rc-kid/rckid/cartridges/demo/sd/files/images/backgrounds/background16.png

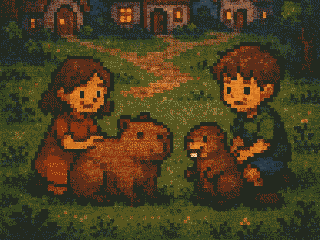
cartridges/demo/sd/files/images/backgrounds/background16.png
