rc-kid/rckid/cartridges/demo/sd/files/images/backgrounds/capybeaver.png

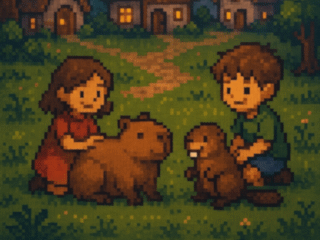
cartridges/demo/sd/files/images/backgrounds/capybeaver.png
