rc-kid/rckid/docs/photos/mkIII-back.jpeg

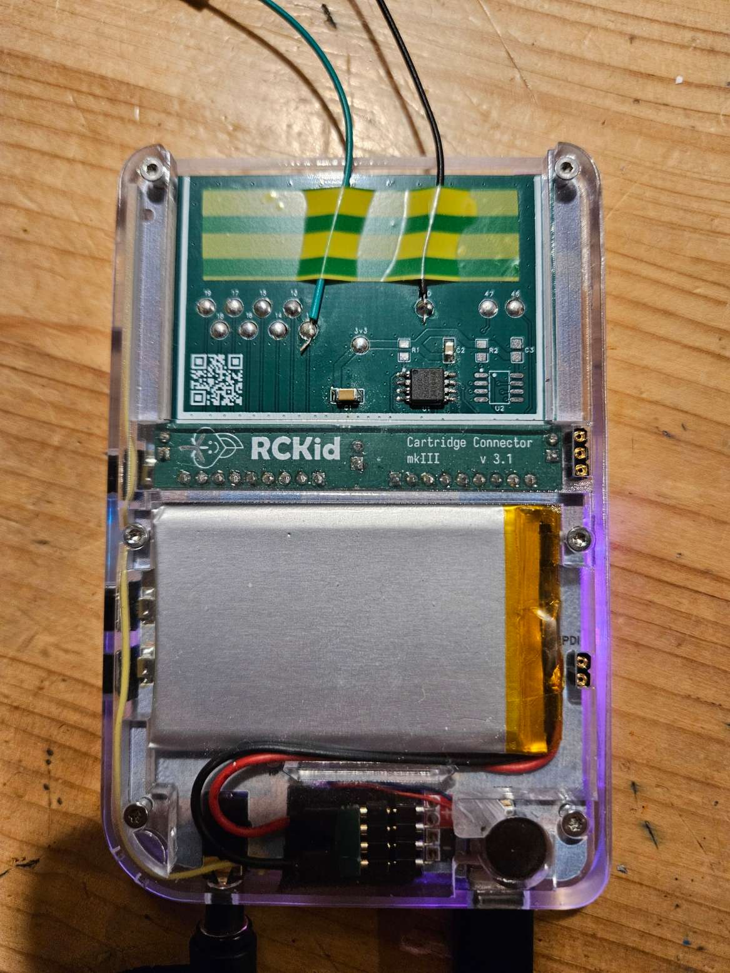
docs/photos/mkIII-back.jpeg
