rc-kid/rckid/docs/photos/mkIII-dark.jpeg

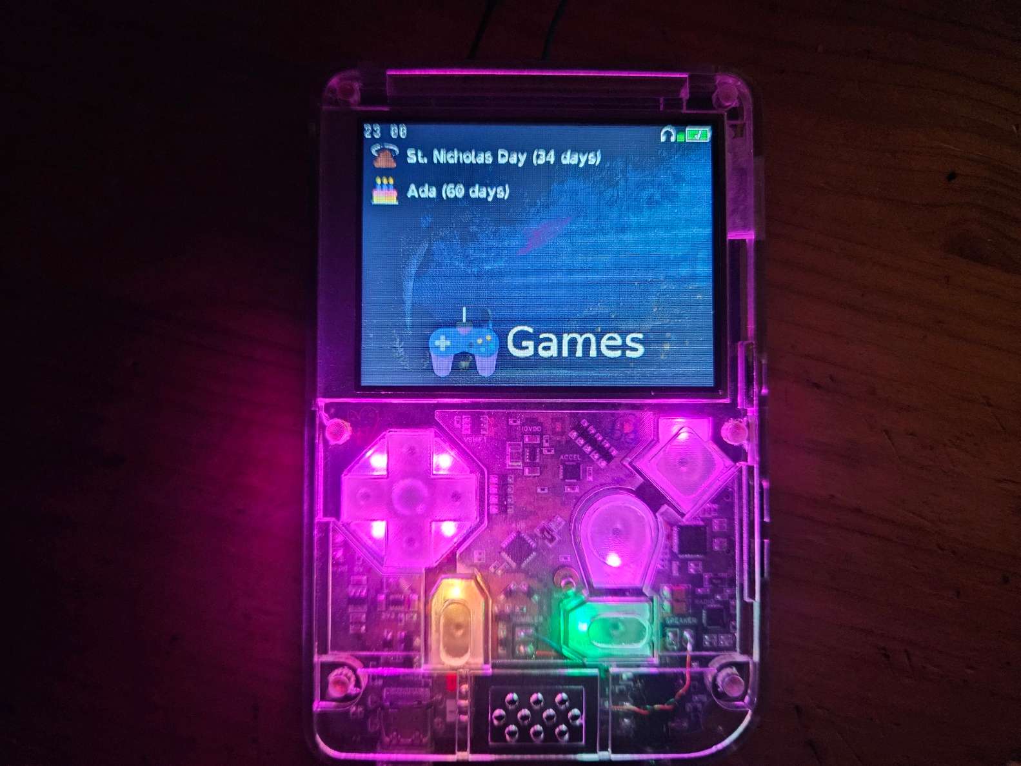
docs/photos/mkIII-dark.jpeg
