rc-kid/rckid/docs/photos/rckid.jpg

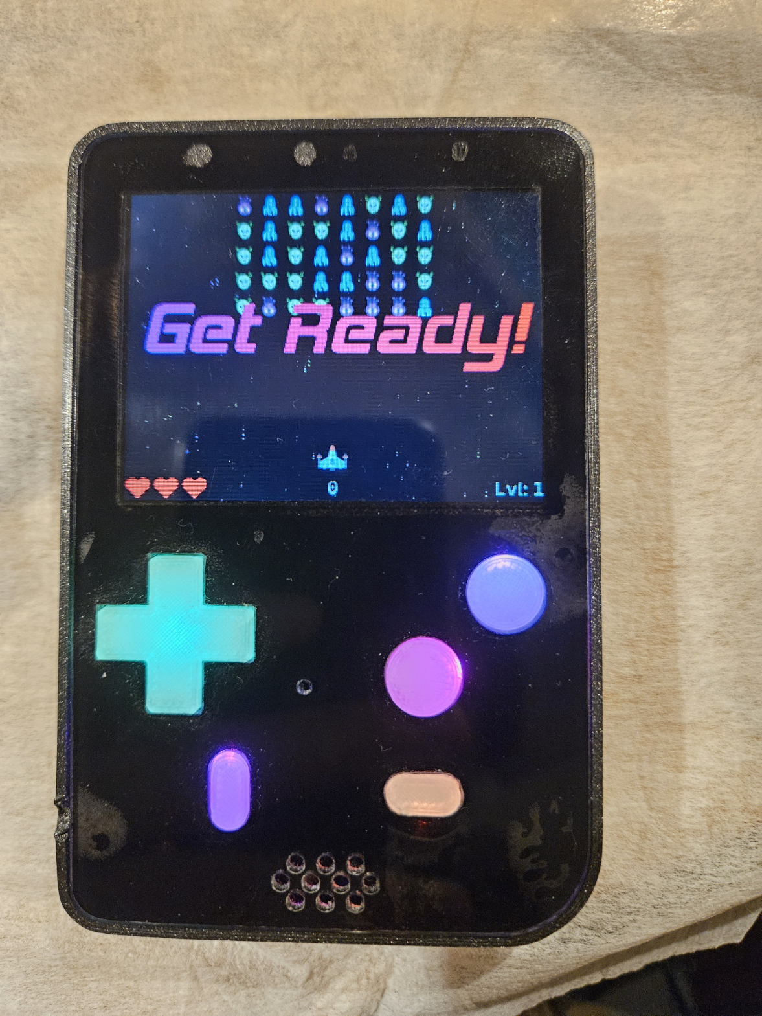
docs/photos/rckid.jpg
