rc-kid/rckid/hardware/images/car.png

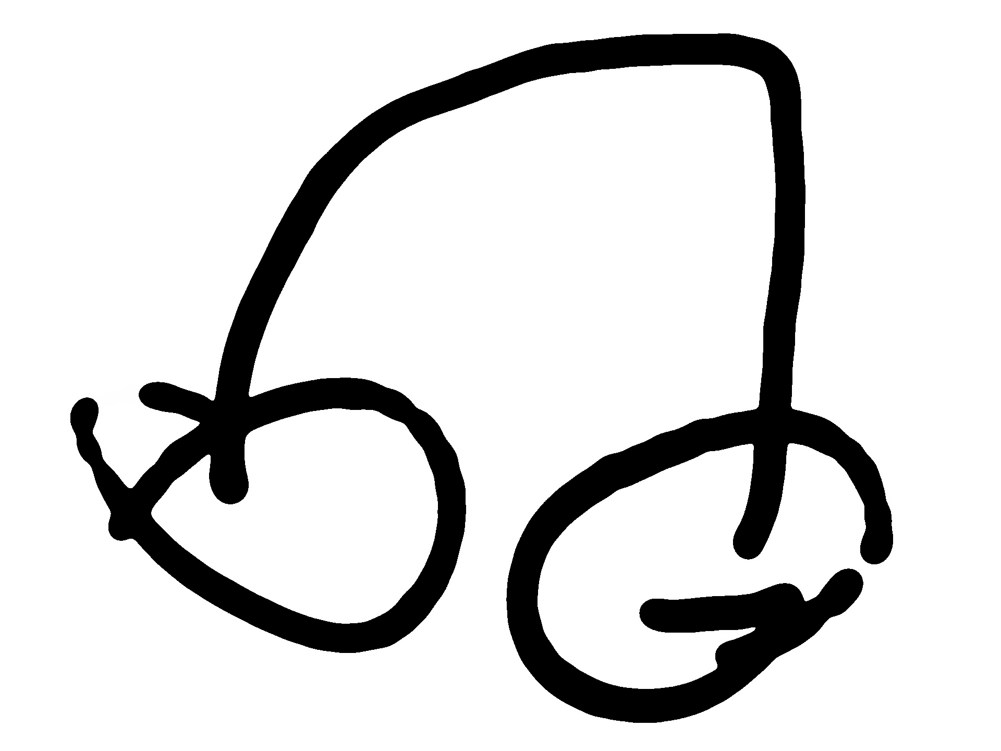
hardware/images/car.png
