rc-kid/rckid/hardware/images/silkscreen-back.png

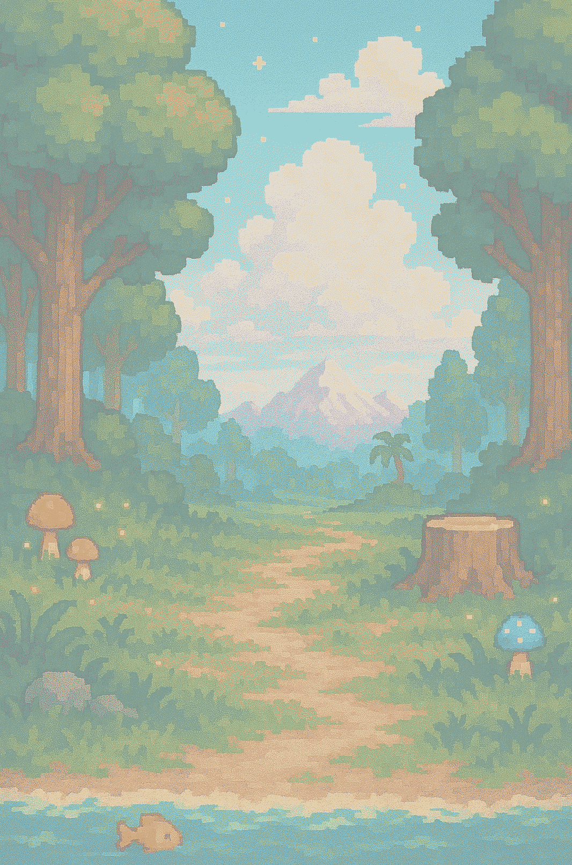
hardware/images/silkscreen-back.png
