rc-kid/rckid/hardware/images/silkscreen-cartridge-ruby.png

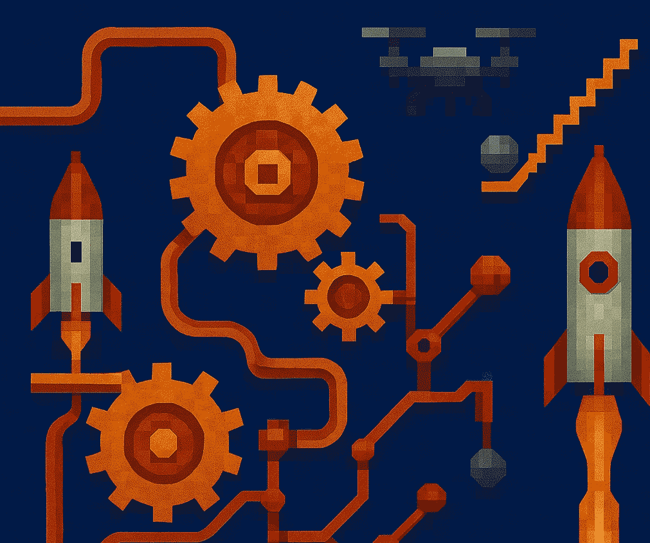
hardware/images/silkscreen-cartridge-ruby.png
