rc-kid/rckid/hardware/images/silkscreen-front-darker.png

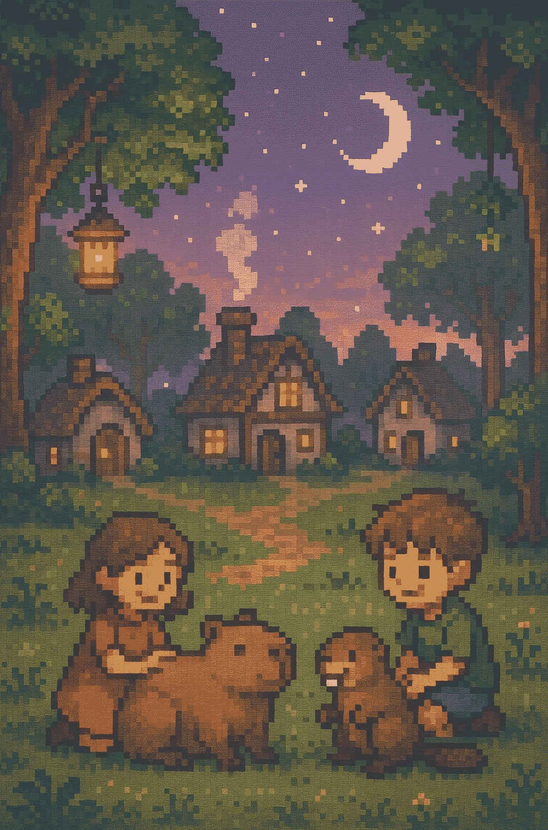
hardware/images/silkscreen-front-darker.png
