rc-kid/rckid/www/background.jpg

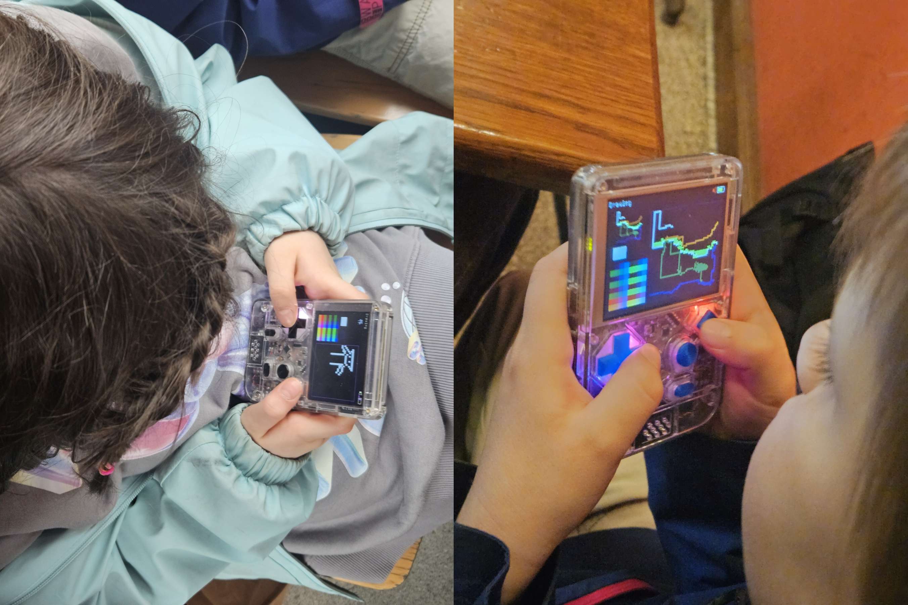
www/background.jpg
