rc-kid/rckid/www/left.jpg

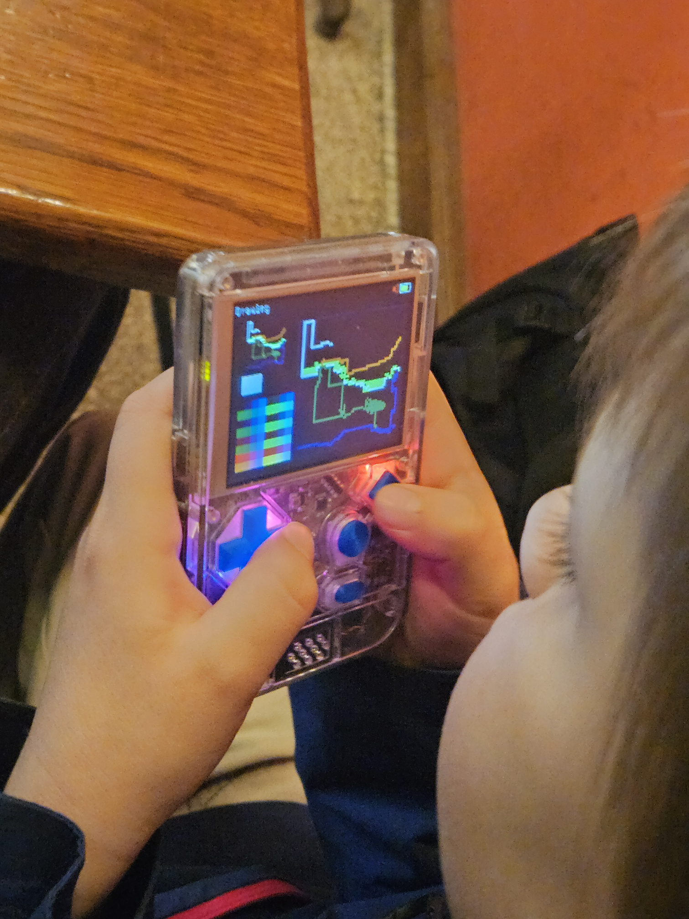
www/left.jpg
