rc-kid/rckid/www/right.jpg

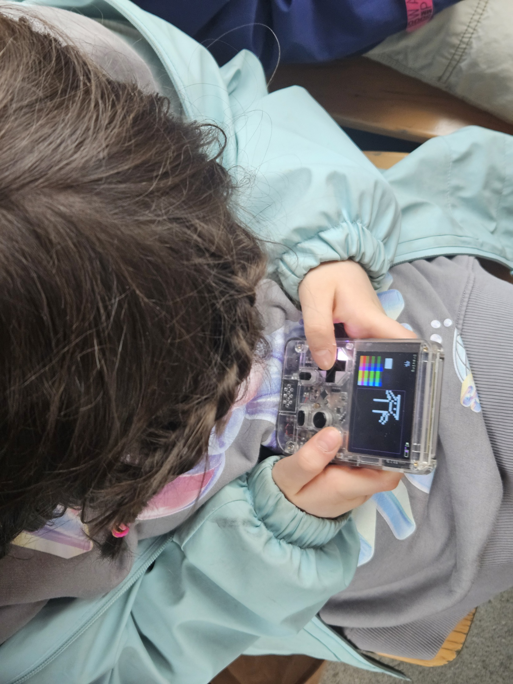
www/right.jpg
