rc-kid/rckid/gbcemu/gbcemu/gbcemu.h

#pragma once

/** When enabled, the emulator will not wait at the end of each frame but would instead run as fast as possible. 
 */
//#define GBCEMU_NO_SPEED_LIMIT


#define GBCEMU_INTERACTIVE_DEBUG 1

#define GBCEMU_ENABLE_BKPT 1

/** Log GBC serial transactions.
 */
#define LL_GBCEMU_SERIAL 0

/** Log GBC rom bank switching.
 */
#define LL_GBCEMU_ROMBANK 0

/** When enabled, every executed instruction will be logged including the state.
 
    While useful for debugging, this is a last resort option as it will slow down the emulator significantly.
 */
#define GBCEMU_TRACE_INSTRUCTIONS 0

/** Very fast very simple tracking of every pc and opcode executed. Note that this only works on fantasy backend as it uses printf for output instead of the debugWrite used elsewhere in rckid's logging.
 */
#define GBCEMU_TRACE_PC_OPCODE 0

#include <rckid/app.h>
#include <rckid/task.h>
#include <rckid/buffer.h>
#include <rckid/fixedint.h>

#include "gamepak.h"
#include "apu.h"

namespace rckid::gbcemu {

    /** GameBoy Color Emulator App
     
        The emulator is an rckid app that consists of the following components organized closely to the original hardware:

        - the cpu, including registers
        - memory (video ram, work ram, cartridge rom, cartridge ram) including bank switching 
        - ppu (pixel processing unit)
        - apu (audio processing unit)


        Most of this builds on a very good GB/GBC reference available at https://gbdev.io/pandocs/About.html
     */
    class GBCEmu : public ModalApp<void> {
    public:

        String name() const override { return STR("GBCEmu_" << appName_); }

        Capabilities capabilities() const override {
            return {
                .canPersistState = true,
                .consumesBudget = true,
                .standalone = true,
            };
        }

        /** GBCEmu version
         
            version 2: adds RTC mapping into the persistent storage, adds support for loading old version values too
         */
        static constexpr uint8_t VERSION = 2;

        static constexpr uint32_t SCALED_WIDTH = 267;
        static constexpr uint32_t SCALED_HEIGHT = 240;

        /** Searches given folder for compatible game ROMs and adds them to the provided menu. 
         
            The menu item actions will start GBCEmu with the selected game loaded as cartridge. Any file with `gb` extension in the provided folder is assumed to be a compatible ROM.
         */
        static void appendGamesFrom(char const * path, ui::Menu * into);

        static unique_ptr<ui::Menu> gamesMenuExtender(unique_ptr<ui::Menu> gamesMenu) {
            appendGamesFrom("/games", gamesMenu.get());
            return gamesMenu;
        }

        enum class DisplayMode {
            Native,
            Scaled,
            X2
        }; 

        GBCEmu(String appName, GamePak * gamepak):
            GBCEmu(std::move(appName)) {
            loadCartridge(gamepak);
        }

        ~GBCEmu() override;
        
        /** Saves the game state to the provided savefile stream. 
         */
        void saveState(RandomWriteStream & into) const override;
        
        /** Loads the game state from the given savefile. 
         */
        bool loadState(RandomReadStream & from) override;

        /** Laods the given gamepak in the emulator. 
         
            This function should only be used during testing, the default constructor with application name and gamepak should be the only user-facing way of starting GBCEmu.
         */
        void loadCartridge(GamePak * game);

        /** Test interface
         */

        /** Main loop of the VM. 
         */
        void loop() override;

        uint32_t elapsedCycles() const { return timerCycles_; }

        uint8_t a() const { return regs8_[REG_INDEX_A]; }
        uint8_t b() const { return regs8_[REG_INDEX_B]; }
        uint8_t c() const { return regs8_[REG_INDEX_C]; }
        uint8_t d() const { return regs8_[REG_INDEX_D]; }
        uint8_t e() const { return regs8_[REG_INDEX_E]; }
        uint8_t h() const { return regs8_[REG_INDEX_H]; }
        uint8_t l() const { return regs8_[REG_INDEX_L]; }
        uint8_t f() const { return regs8_[REG_INDEX_F]; }

        uint16_t af() const { return regs16_[REG_INDEX_AF]; }
        uint16_t bc() const { return regs16_[REG_INDEX_BC]; }
        uint16_t de() const { return regs16_[REG_INDEX_DE]; }
        uint16_t hl() const { return regs16_[REG_INDEX_HL]; }

        uint16_t pc() const { return pc_; }
        uint16_t sp() const { return sp_; }

        bool flagZ() const { return regs8_[REG_INDEX_F] & FLAG_Z; }
        bool flagN() const { return regs8_[REG_INDEX_F] & FLAG_N; }
        bool flagH() const { return regs8_[REG_INDEX_F] & FLAG_H; }
        bool flagC() const { return regs8_[REG_INDEX_F] & FLAG_C; }

        bool ime() const { return ime_; }
        uint8_t ie() const;

        void setState(uint16_t pc, uint16_t sp, uint16_t af, uint16_t bc, uint16_t de, uint16_t hl, bool ime, uint8_t im);

        void writeMem(uint16_t address, std::initializer_list<uint8_t> values);

        uint8_t readMem(uint16_t address);

        /** Performs single instruction step and returns the number of cycles it took. 
         */
        uint32_t step();

#ifdef GBCEMU_INTERACTIVE_DEBUG

        uint32_t instructionSize(uint8_t opcode) const ; 

        uint16_t breakpoint() const { return breakpoint_; }
        void setBreakpoint(uint16_t address) { breakpoint_ = address; }

        uint16_t memoryBreakpointStart() const { return memoryBreakpointStart_; }
        uint16_t memoryBreakpointEnd() const { return memoryBreakpointEnd_; }
        void setMemoryBreakpoint(uint16_t start, uint16_t end) { 
            memoryBreakpointStart_ = start; 
            memoryBreakpointEnd_ = end;
        }

        /** Disassembles the given section on memory as assembly instructions. 
         */
        void logDisassembly(uint16_t start, uint16_t end);

        /** Disassembles the given memory section as raw data. 
         */
        void logMemory(uint16_t start, uint16_t end);

        void logStack(uint32_t n);

        void logVisited();

        /** Logs the current state of the emulator. 
         */
        void logState(); 

        void clearTilemap();
        void setTilemap(uint32_t x, uint32_t y, uint8_t tile);

        void clearTileset();
        void setTile(uint8_t index, uint8_t * data);
#endif

    protected:

        GBCEmu(String appName);

        /** Clears all the structures asociated with GBCEmu. Useful for teardown, or between cartridge swaps. 
         */
        void clear();

        void onFocus() override;
        void onBlur() override;

        /** Render does nothing as drawing is part of the emulators custom loop, but as it is abstract in the base class, we have to define something. 
         */
        void render() override { }

        /** Clears the gamepak caches to free up memory 
         */        
        void releaseResources() override;

        /** Returns the home menu
         
            TODO
         */
        unique_ptr<ui::Menu> homeMenu() override;

        /** Saves the external RAM to the app folder. 
         */
        void saveExternalRam();

        /** Loads the external RAM from the app folder. 
         */
        void loadExternalRam();

        /** Returns the number of ROM pages available in the current cartridge.
         */
        uint32_t romPages() const { return gamepak_->cartridgeROMSize() / 16384; }

        /** Returns the number of external RAM pages available in the current cartridge.
         */
        uint32_t externalRamPages() const { return gamepak_->cartridgeRAMSize() / 8192; }


    private:

        /** \name Arithmetic helpers
         
            Helper arithmetic functions called from the instruction implementations in insns.inc.h.
         */
        //@{

        FORCE_INLINE(uint8_t inc8(uint8_t x));
        FORCE_INLINE(uint8_t dec8(uint8_t x));
        FORCE_INLINE(uint8_t add8(uint8_t a, uint8_t b, uint8_t c = 0));
        FORCE_INLINE(uint8_t sub8(uint8_t a, uint8_t b, uint8_t c = 0));
        FORCE_INLINE(uint16_t add16(uint16_t a, uint16_t b));
        FORCE_INLINE(uint8_t rlc8(uint8_t a));
        FORCE_INLINE(uint8_t rl8(uint8_t a));
        FORCE_INLINE(uint8_t rrc8(uint8_t a));
        FORCE_INLINE(uint8_t rr8(uint8_t a));
        FORCE_INLINE(uint8_t sla8(uint8_t a));
        FORCE_INLINE(uint8_t sra8(uint8_t a));
        FORCE_INLINE(uint8_t srl8(uint8_t a));

        //@}

        /** \name CPU 
         
            The following 8 bit registers are available:

            - A (accumulator)
            - F (flags), only few bits available as the ZNHC flags. 
            - B, C, D, E, H, L general purpose 8bit registers
        
            The AF, BC, DE and HL registers are 16bit wide and share the same space with their 8bit counterparts.

            Dedicated 16bit registers are:

            - SP (stack pointer)
            - PC (program counter)
         */
        //@{
        static constexpr uint32_t REG_INDEX_A = 1;
        static constexpr uint32_t REG_INDEX_F = 0;
        static constexpr uint32_t REG_INDEX_B = 3;
        static constexpr uint32_t REG_INDEX_C = 2;
        static constexpr uint32_t REG_INDEX_D = 5;
        static constexpr uint32_t REG_INDEX_E = 4;
        static constexpr uint32_t REG_INDEX_H = 7;
        static constexpr uint32_t REG_INDEX_L = 6;

        static constexpr uint32_t REG_INDEX_AF = 0;
        static constexpr uint32_t REG_INDEX_BC = 1;
        static constexpr uint32_t REG_INDEX_DE = 2;
        static constexpr uint32_t REG_INDEX_HL = 3;

        union {
            uint8_t regs8_[8];
            uint16_t regs16_[4];
        }; 

        uint16_t sp_;
        uint16_t pc_;

        /** True if CGB mode is enabled. This is twice the speed and some extra capabilities in rendering, etc. 
         */
        bool cgb_ = false;

        /** Flags. 
         
            - `Z` (zero flag) set only if the actual result is 0
            - `N` (subtract flag) set to a constant it seems
            - `H` (half carry flag) 
            - `C` (carry flag)
         */
        static constexpr uint8_t FLAG_Z = 1 << 7;
        static constexpr uint8_t FLAG_N = 1 << 6;
        static constexpr uint8_t FLAG_H = 1 << 5;
        static constexpr uint8_t FLAG_C = 1 << 4;   

        void setFlagZ(bool value) { value ? regs8_[REG_INDEX_F] |= FLAG_Z : regs8_[REG_INDEX_F] &= ~FLAG_Z; }

        void setFlagN(bool value) { value ? regs8_[REG_INDEX_F] |= FLAG_N : regs8_[REG_INDEX_F] &= ~FLAG_N; }

        void setFlagH(bool value) { value ? regs8_[REG_INDEX_F] |= FLAG_H : regs8_[REG_INDEX_F] &= ~FLAG_H; }

        void setFlagC(bool value) { value ? regs8_[REG_INDEX_F] |= FLAG_C : regs8_[REG_INDEX_F] &= ~FLAG_C; }

        void stackFramePush() {
            sp_ -= 2;
            memWr16(sp_, pc_);
        }

        void stackFramePop() {
            pc_ = memRd16(sp_);
            sp_ += 2;
        }

        /** Takes the GBC relative address and converts it to a unique number that can be used for absolute addressing including banks, etc
         */
        uint32_t convertAddressToAbsolute(uint16_t addr);

        void runCPU(uint32_t cycles);
        //@}

        /** Memory.
         
            GBC provides the following memories:

            - 16KB video ram, banked by 8KB
            - 32KB work ram, banked by 4KB
            - cartridge ROM, up to 8MB, banked by 16KB
            - cartridge RAM, up to 128KB, banked by 8KB

            Since only 64KB can be addressed at time, memory mapping is a must. To access cartridge data larger than 32KB, a memory mapper chip must be present in the cartridge. 

            # Memory Map

            0x0000 | 0x3fff | 16KB  | 0..3   | ROM Bank 00, from cartridge, usually fixed bank
            0x4000 | 0x7fff | 16KB  | 4..7   | ROM bank 01-NN, from cartridge, switchable by mapper chip if any
            0x8000 | 0x9fff |  8KB  | 8,9    | Video RAM
            0xa000 | 0xbfff |  8KB  | 10, 11 | External RAM
            0xc000 | 0xcfff |  4KB  | 12     | WRAM bank 0
            0xd000 | 0xdfff |  4KB  | 13     | WRAM bank 1..7
            0xe000 | 0xfdff |  <8KB | 14, 15 | Echo ram, mirror of 0xc000..0xddff, prohibited
            0xfe00 | 0xfe9f |  160  |        | OAM memory
            0xfea0 | 0xfeff |       |        | Prohibited
            0xff00 | 0xff7f | 128   |        | IO Registers
            0xff80 | 0xfffe | 127   |        | High RAM 
            0xffff | 0xffff | 1     |        | Interrupt enable register   
            
            The memory is divided into 16 4KB blocks, with the last block being a bit more complex as it contains echo ram, oam memory, io regs and hram. Furthemore, all allocations of RAM memories are done in 4KB blocks as well to limit fragmentation due to possibly large allocatons in case of big memories. 
         */

        static constexpr uint8_t MEMMAP_VRAM_0 = 8;
        static constexpr uint8_t MEMMAP_VRAM_1 = 9;
        static constexpr uint16_t ERAM_START = 0xa000;

        /** Reads one byte from memory. For most reads & writes this simply goes through the memmap, but there are special cases for the shorter memory blocks towards the end of the address space.
         */
        uint8_t memRd8(uint16_t addr);

        /** Reads a 16bit value. 
         */
        uint16_t memRd16(uint16_t addr);

        void memWr8(uint16_t addr, uint8_t value);
        void memWr16(uint16_t addr, uint16_t value);


        void writeRom(uint16_t addr, uint8_t value);

        void writeERam(uint16_t offset, uint8_t value);
        uint8_t readERam(uint16_t offset);

        /** Sets the specific IO register, or HRAM.
         */
        void setIORegisterOrHRAM(uint32_t addr, uint8_t value);

        /** Sets the second ROM page to the given address. The address must point to a consecutive 16KB bytes long array. 
         */
        void setRomPage(uint32_t page);
        uint32_t getRomPage() const;

        /** Sets the video ram page. Video ram pages are 8 KB and two of them are available for GBC. 
         */
        void setVideoRamPage(uint32_t page);
        uint32_t getVideoRamPage() const;

        /** Sets the second work ram page (first is always 0). GBC has 8 work ram banks, banks 1 to 7 can be mapped here.
         */
        void setWorkRamPage(uint32_t page);
        uint32_t getWorkRamPage() const;

        /** Sets external ram bank. Valid values are from 0 to 16, external ram banks are 8KB in size.
         */
        void setExternalRamPage(uint32_t page); 
        uint32_t getExternalRamPage() const;


        /** Faster memory reads for program counter where we assume the address does not belong to the 16th bank with oam and high mem. 
         */
        uint8_t mem8(uint16_t addr);
        uint16_t mem16(uint16_t addr);

        uint8_t * vram_[2] = { 0,0 };
        uint8_t * wram_[8] = { 0,0,0,0,0,0,0,0 };
        uint8_t * oam_ = nullptr;
        uint8_t * hram_ = nullptr;

        // eram of up to 128kb (16 banks of 8kb)
        uint8_t * eram_[16] = { 0,0,0,0,0,0,0,0,0,0,0,0,0,0,0,0 };
        bool eramActive_ = false;

        static constexpr uint8_t RTC_MAPPING_NONE = 0x00;
        static constexpr uint8_t RTC_MAPPING_SECONDS = 0x08;
        static constexpr uint8_t RTC_MAPPING_MINUTES = 0x09;
        static constexpr uint8_t RTC_MAPPING_HOURS = 0x0a;
        static constexpr uint8_t RTC_MAPPING_DAYS_LOW = 0x0b;
        static constexpr uint8_t RTC_MAPPING_DAYS_HIGH = 0x0c;

        uint8_t rtcMapping_ = RTC_MAPPING_NONE;

        // memory mapping information. For fast access, the memory is divided into 16 4kb regions with pointers to beginning in the array. This is true for all but the last block, which is a bit more complex as it contains echo ram, oam memory, io regs and hram.
        uint8_t * memMap_[16] = { 0,0,0,0,0,0,0,0,0,0,0,0,0,0,0,0 };

        // MBC type used in the current gamepak
        MBC mbc_ = MBC::None;
        uint32_t romPage_ = 1;

        /** \name Controls
         
            Controls are really simple, the IO_JOYP register controls both the dpad and the buttons as well as selecting whether it is the dpad or the buttons that will be actively monitored. An interrupt is requested whenever a lower bit goes from high to low. 

            Important to note is that button bit being 0 means the button is pressed, while high means released. There is apparently no HW debouncing on the gameboy so multiple presses are possible. 
         
            TODO this function should be called regularly at each tick to update the IO_JOYP register with any changes in the button state. 
         */
        //{
        void updateIO_JOYP();
        //} 

        /** \name Timer
         */
        //@{
        void updateTimer();

        uint32_t timerDIVModulo_ = 255;
        uint32_t timerTIMAModulo_ = 0;
        uint32_t timerCycles_ = 0;
        //@}



        /** \name PPU
     
            The PPU rendering happens in dots. One dot corresponds to 1 clock cycle on Original gameboy, or 2 clock cycles on the faster GBC. There are 144 scanlines with 160 pixels per scanline. Each scanline consists of 456 dots, which are distributed as follows:

            - Mode 2: 80 dots are spent in OAM scan (OAM inaccessible)
            - Mode 3: 172-289 dots for drawing pixel data  (OAM and VRAM inaccessible)
            - Mode 0: 87-204 dots for hblank

            The vblank itself is 4560 dots (10 lines), called Mode 1, during which all memory is accessible (same as hblank). 
         */
        //@{

        /** Object Attribute Memory for a single sprite.
         
            Each sprite contains its x and y values, tile number and flags (priority, palettes, flips, etc.). Important note is that the sprite y coordinate is offset by 16 pixels, so the actual sprite y position is y - 16.
         */
        PACKED(struct OAMSprite {
            uint8_t y_;
            uint8_t x_;
            uint8_t tile;
            uint8_t flags;

            int32_t y() const { return y_ - 16; }
            int32_t x() const { return x_ - 8; }

            bool priority() const { return flags & 0x80; }
            bool yFlip() const { return flags & 0x40; }
            bool xFlip() const { return flags & 0x20; }
            uint8_t palette() const { return flags & 0x10; }
            uint8_t bank() const { return flags & 0x08; }
            uint8_t cgbPalette() const { return flags & 0x07; }
        });

        static_assert(sizeof(OAMSprite) == 4);

        static constexpr uint32_t NUM_SPRITES = 40;
        static constexpr uint32_t DOTS_PER_LINE = 456;
        static constexpr uint32_t DOTS_MODE_2 = 80;
        static constexpr uint32_t DOTS_MODE_3 = 172;
        static constexpr uint32_t DOTS_MODE_0 = 204;
        
        void initializeDisplay();

        void setPPUMode(unsigned mode);
       
        void moveToNextScanline();

        /** Graphics rendering for a single line.
         */
        void renderLine();

        DisplayMode displayMode_ = DisplayMode::Scaled;
        uint32_t displayX2Start_ = 0;
        //@}

        // APU implementation
        APU apu_;

        // name of the cartridge used
        String appName_;

        // Current gamepak
        GamePak * gamepak_ = nullptr;

        // interrupts enabled flag (cannot be read, only set by insns)
        // TODO is this necessary or can I just use the last high mem byte?
        bool ime_ = false;

#ifdef GBCEMU_INTERACTIVE_DEBUG
        // breakpoint at which the main loop pauses
        bool debug_ = false;
        uint16_t breakpoint_ = 0xffff;
        uint16_t memoryBreakpointStart_ = 0xffff;
        uint16_t memoryBreakpointEnd_ = 0xffff;
        uint32_t overBreakpoint_ = 0xffffff;
        uint8_t visitedInstructions_[64];

        uint32_t disassembleInstruction(uint16_t addr, bool state = false);
        void markAsVisited(uint16_t pc);
        void resetVisited();
        void debugInteractive();
#endif

        DoubleBuffer<Color::RGB565> pixels_;
        DoubleBuffer<Color::RGB565> pixelsBackup_;
        Coord displayY_;

        Color::RGB565 palette_[4] = {
            // the default DMG green palette
            Color::RGB(155, 188, 15).toRGB565(),
            Color::RGB(139, 172, 15).toRGB565(),
            Color::RGB(48, 98, 48).toRGB565(),
            Color::RGB(15, 56, 15).toRGB565(),            
            // Game Boy Pocket-ish palette
            /*
            ColorRGB{255, 255, 255}, 
            ColorRGB{170, 170, 170},
            ColorRGB(85, 85, 85),
            ColorRGB{0,0,0},
            */
            // white on black palette
            /*
            ColorRGB{0,0,0},
            ColorRGB(85, 85, 85),
            ColorRGB{170, 170, 170},
            ColorRGB{255, 255, 255}, 
            */
        };


        /** Nearest Neighbor Precalculations 
          
            To facilitate fast scaling to the entire screen, we have nearest neighbor calculations precomputed for cols and rows separately. Those two arrays tell the renderer for each native pixel how many columns and how many rows it will take when scaled. 
         
            The algorithm then rescales each line according to the colScaling_ values and sends it to the display either once, or twice, depending on the rowScaling_ values. 
         */
        static constexpr uint8_t rowScaling_[144] = {
#include "rowScaling.inc.h"
        };

        static constexpr uint8_t colScaling_[160] = {
#include "colScaling.inc.h"
        };
            
    }; // rckid::gbcemu::GBCEmu


} // namespace rckid::gbcemu
