rc-kid/rckid/gbcemu/gbcemu/gamepak_type.inc.h

CTYPE(0x00,	ROM_ONLY,                       MBC::None)
CTYPE(0x01,	MBC1,                           MBC::Type1)
CTYPE(0x02,	MBC1_RAM,                       MBC::Type1)
CTYPE(0x03,	MBC1_RAM_BATTERY,               MBC::Type1)
CTYPE(0x05,	MBC2,                           MBC::Type2)
CTYPE(0x06,	MBC2_BATTERY,                   MBC::Type2)
CTYPE(0x08,	ROM_RAM,                        MBC::None)
CTYPE(0x09,	ROM_RAM_BATTERY,                MBC::None)
CTYPE(0x0B,	MMM01,                          MBC::MMM01)
CTYPE(0x0C,	MMM01_RAM,                      MBC::MMM01)
CTYPE(0x0D,	MMM01_RAM_BATTERY,              MBC::MMM01)
CTYPE(0x0F,	MBC3_TIMER_BATTERY,             MBC::Type3)
CTYPE(0x10,	MBC3_TIMER_RAM_BATTERY,         MBC::Type3)
CTYPE(0x11,	MBC3,                           MBC::Type3)
CTYPE(0x12,	MBC3_RAM,                       MBC::Type3)
CTYPE(0x13,	MBC3_RAM_BATTERY,               MBC::Type3)
CTYPE(0x19,	MBC5,                           MBC::Type5)
CTYPE(0x1A,	MBC5_RAM,                       MBC::Type5)
CTYPE(0x1B,	MBC5_RAM_BATTERY,               MBC::Type5)
CTYPE(0x1C,	MBC5_RUMBLE,                    MBC::Type5)
CTYPE(0x1D,	MBC5_RUMBLE_RAM,                MBC::Type5)
CTYPE(0x1E,	MBC5_RUMBLE_RAM_BATTERY,        MBC::Type5)
CTYPE(0x20,	MBC6,                           MBC::Type6)
CTYPE(0x22,	MBC7_SENSOR_RUMBLE_RAM_BATTERY, MBC::Type7)
CTYPE(0xFC,	POCKET_CAMERA,                  MBC::Other)
CTYPE(0xFD,	BANDAI_TAMA5,                   MBC::Other)
CTYPE(0xFE,	HuC3,                           MBC::HuC3)
CTYPE(0xFF,	HuC1_RAM_BATTERY,               MBC::HuC1)

#undef CTYPE
