rc-kid/rckid/gbcemu/tests/startup.cpp

#include "gbctests.h"

namespace rckid::gbcemu {

    TEST(gbcemu, startup_flags) {
        GBCEmu gbc{"", nullptr};
        RUN(
            NOP,
        );
        EXPECT_FLAGS(Z);
    }

} // namespace rckid::gbcemu
